likematthew/ExOrShock/3D Object/V2/Shaker.jpg

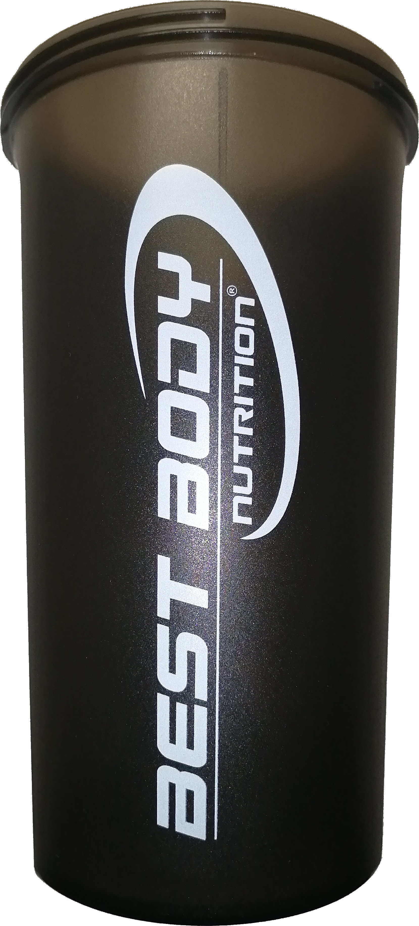
3D Object/V2/Shaker.jpg
