likematthew/ExOrShock/Project/Images/ex-or-shock-1-5-volt-battery-holder-2.jpg

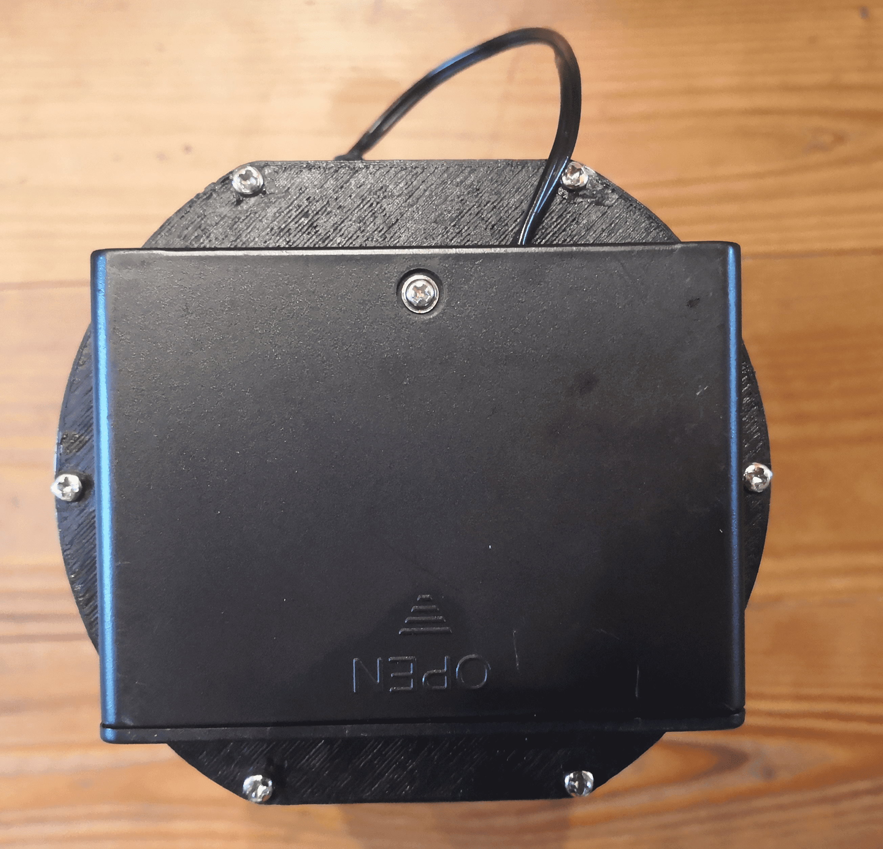
Project/Images/ex-or-shock-1-5-volt-battery-holder-2.jpg
