likematthew/ExOrShock/Project/Images/ex-or-shock-9-volt-battery-1.jpg

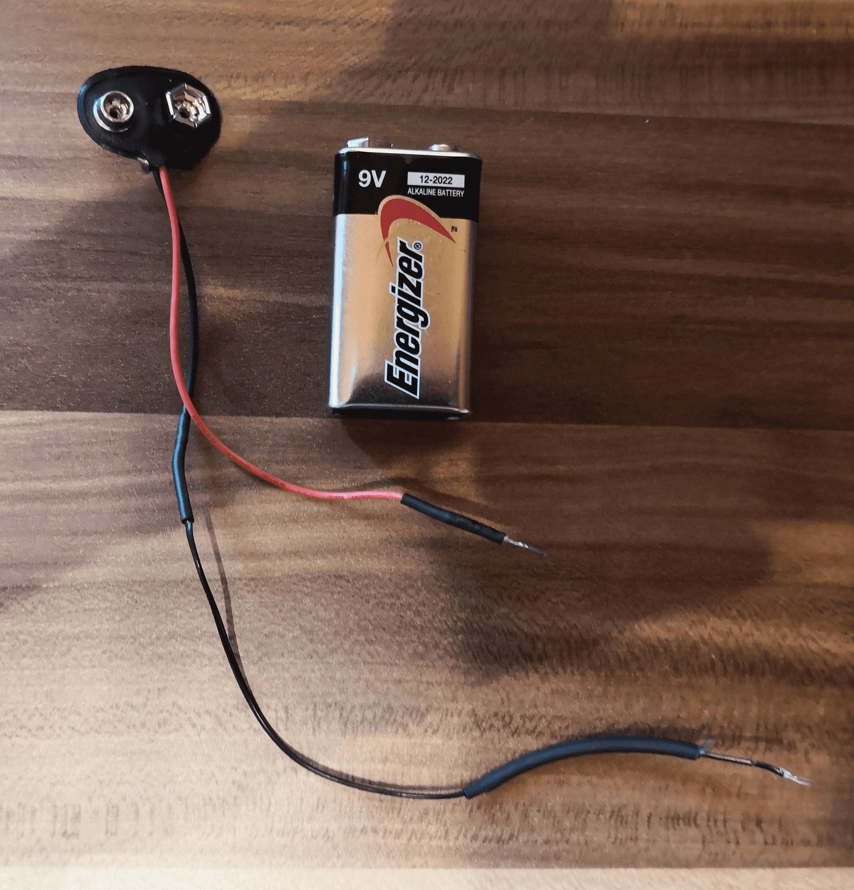
Project/Images/ex-or-shock-9-volt-battery-1.jpg
