likematthew/ExOrShock/Project/Images/ex-or-shock-cup-inside-1.jpg

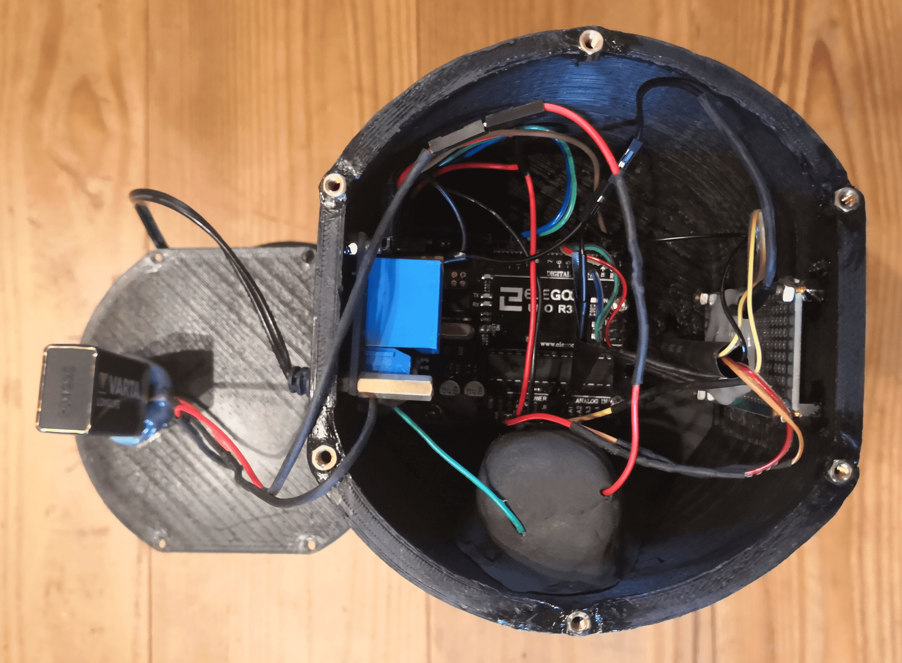
Project/Images/ex-or-shock-cup-inside-1.jpg
