likematthew/ExOrShock/Project/Images/ex-or-shock-cup-inside-2.jpg

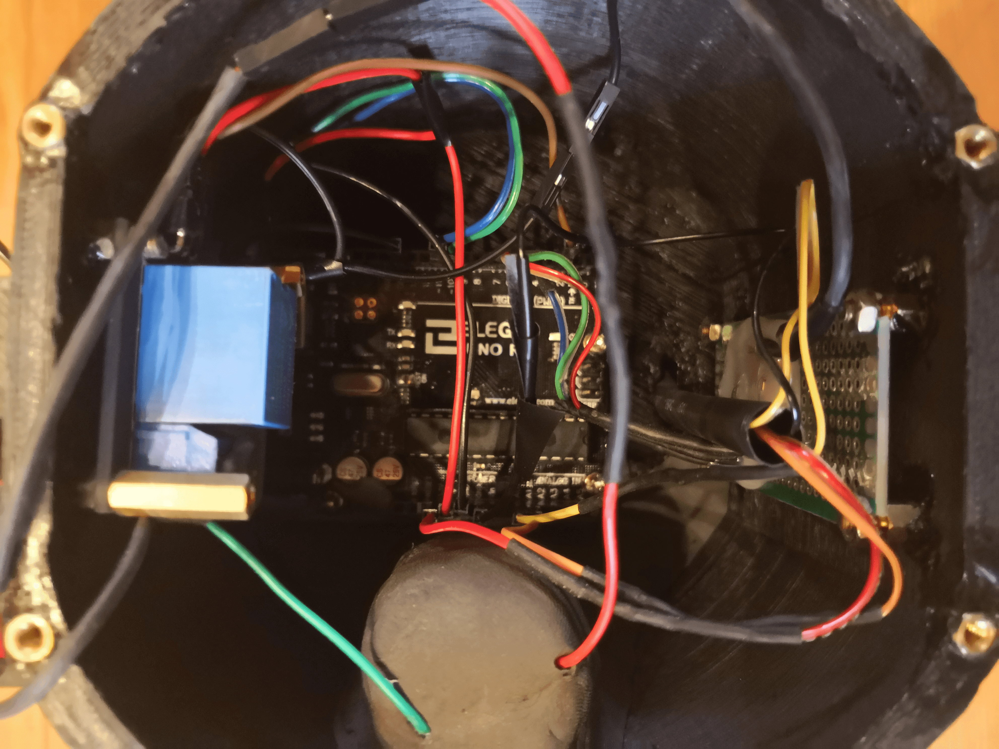
Project/Images/ex-or-shock-cup-inside-2.jpg
