likematthew/ExOrShock/Project/Images/ex-or-shock-cup-outside-1.jpg

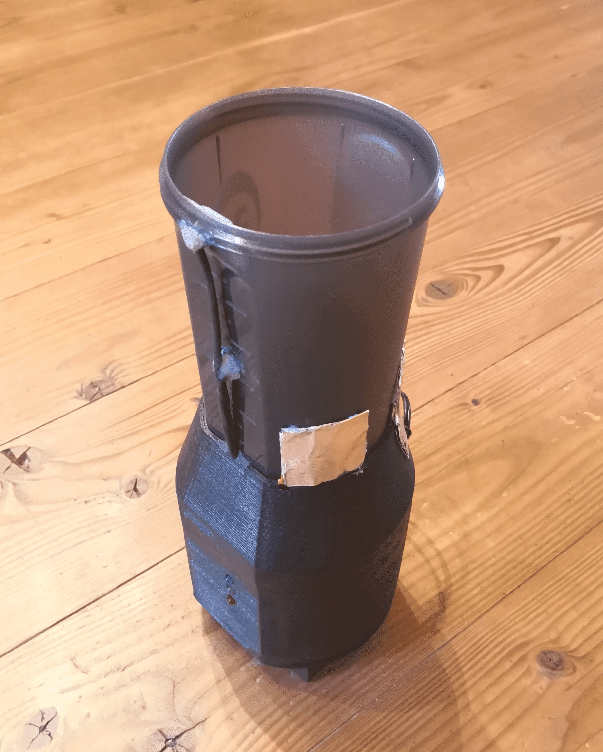
Project/Images/ex-or-shock-cup-outside-1.jpg
