likematthew/ExOrShock/Project/Images/ex-or-shock-fritzing-1.jpg

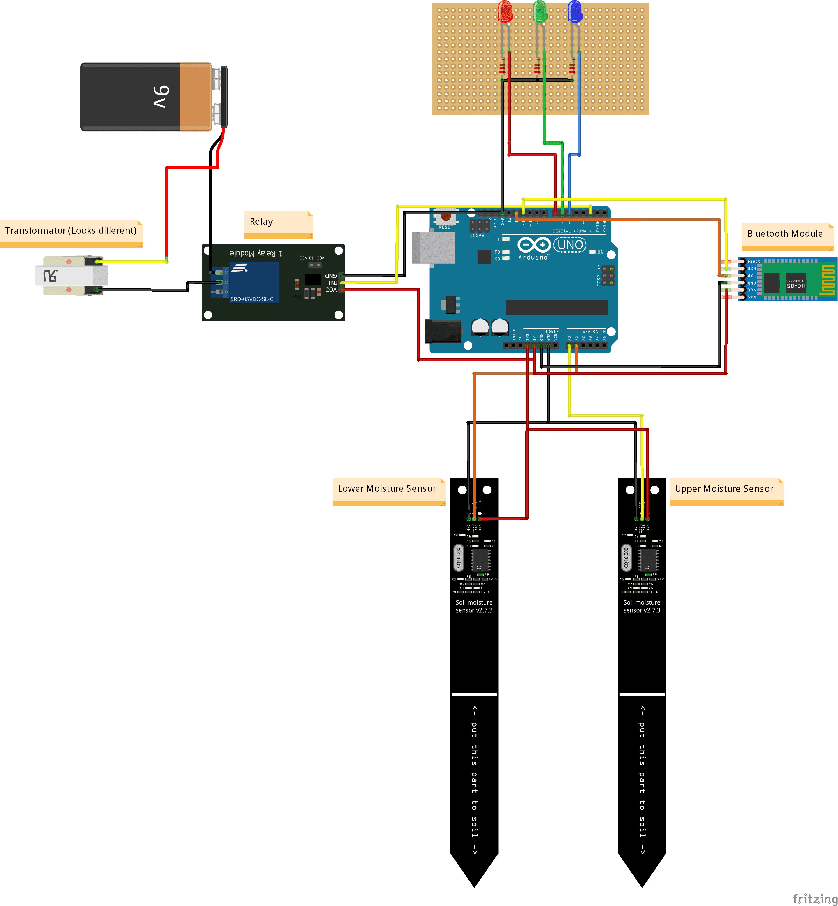
Project/Images/ex-or-shock-fritzing-1.jpg
