likematthew/ExOrShock/Project/Images/ex-or-shock-handle-1.jpg

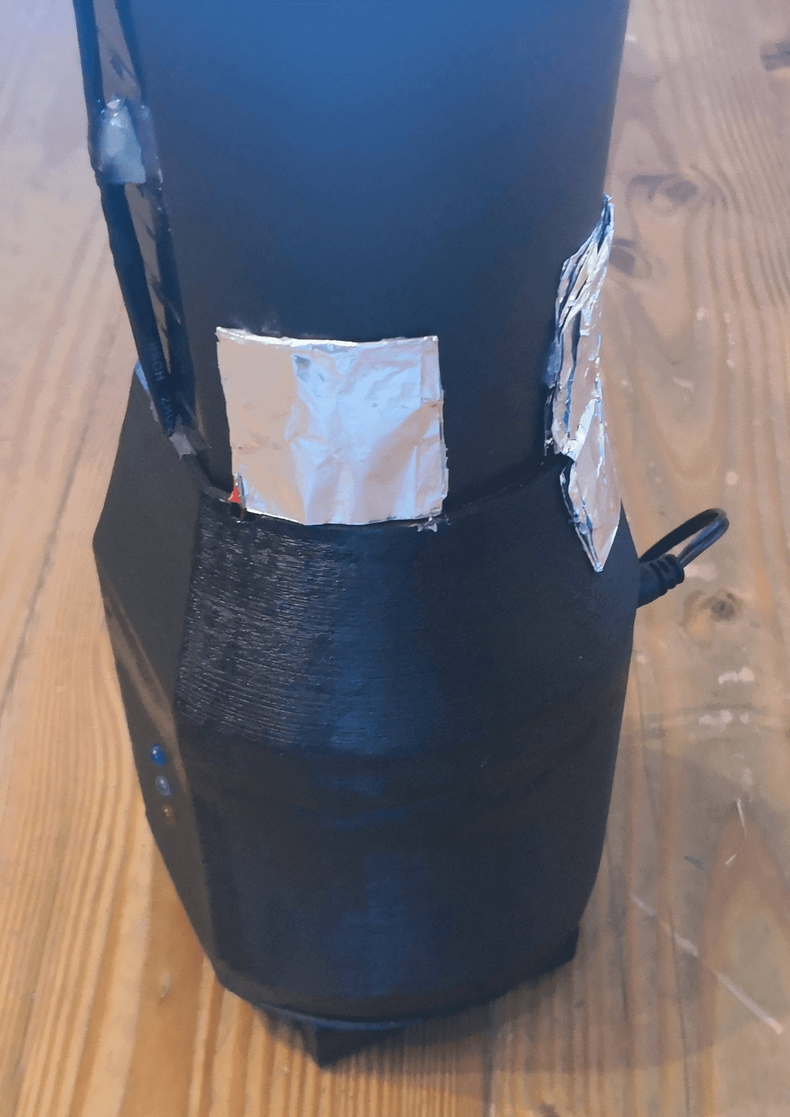
Project/Images/ex-or-shock-handle-1.jpg
