likematthew/ExOrShock/Project/Images/ex-or-shock-handle-2.jpg

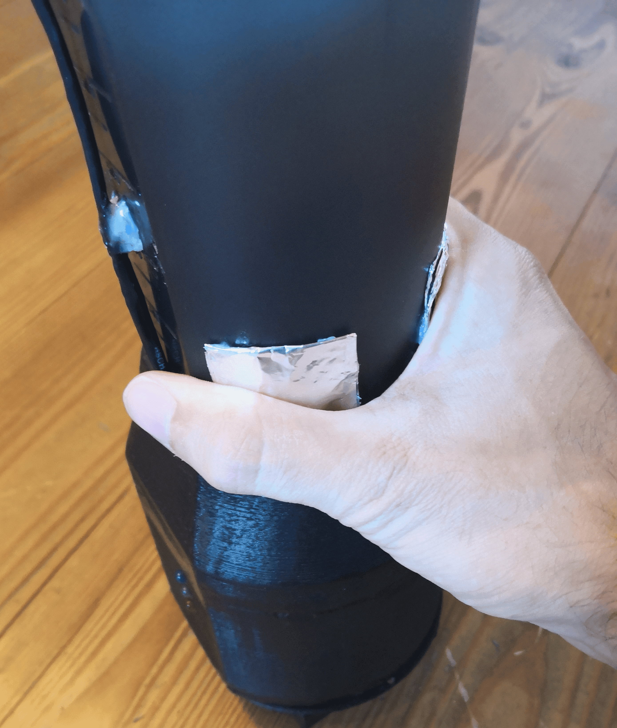
Project/Images/ex-or-shock-handle-2.jpg
