likematthew/ExOrShock/Project/Images/ex-or-shock-housing-1.jpg

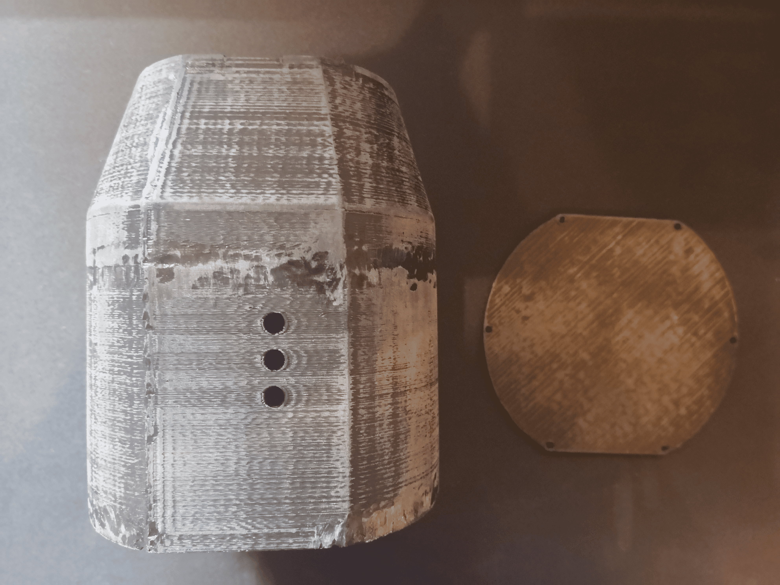
Project/Images/ex-or-shock-housing-1.jpg
