likematthew/ExOrShock/Project/Images/ex-or-shock-housing-2.jpg

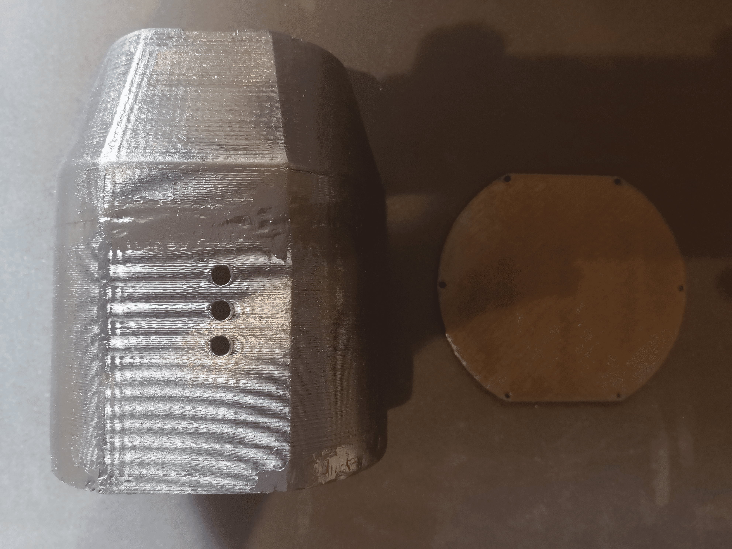
Project/Images/ex-or-shock-housing-2.jpg
