likematthew/ExOrShock/Project/Images/ex-or-shock-housing-moisture-level-sensor-2.jpg

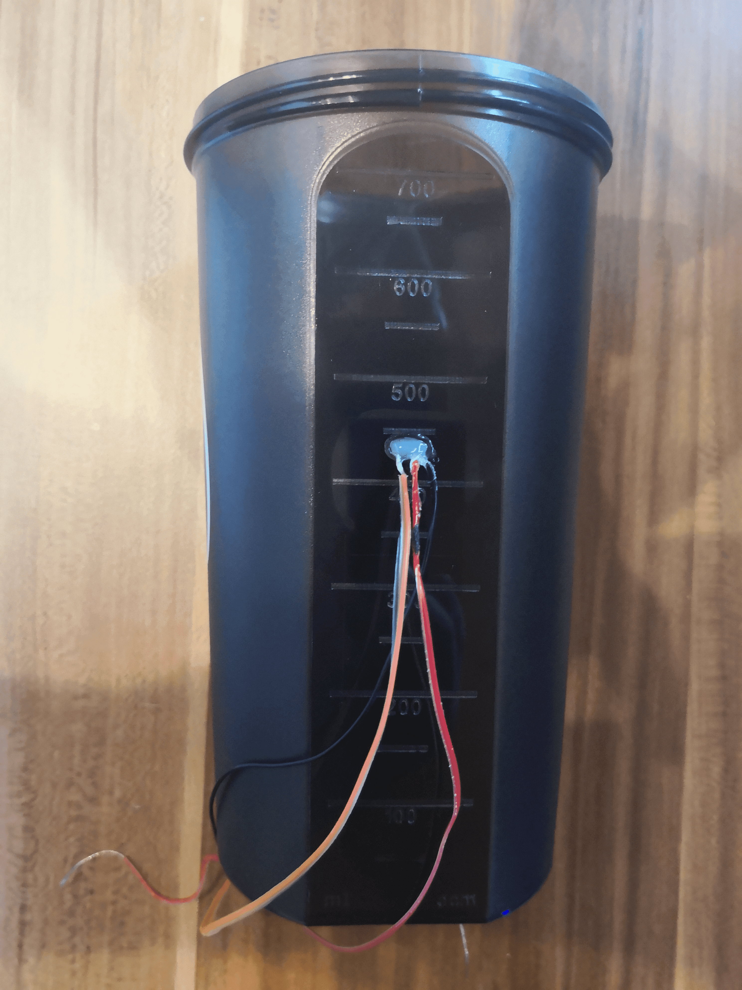
Project/Images/ex-or-shock-housing-moisture-level-sensor-2.jpg
