likematthew/ExOrShock/Project/Images/ex-or-shock-housing-threads-1.jpg

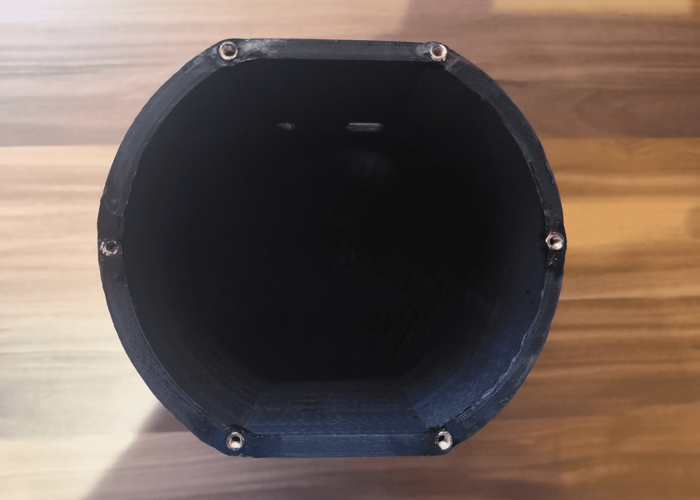
Project/Images/ex-or-shock-housing-threads-1.jpg
