likematthew/ExOrShock/Project/Images/ex-or-shock-housing-threads-3.jpg

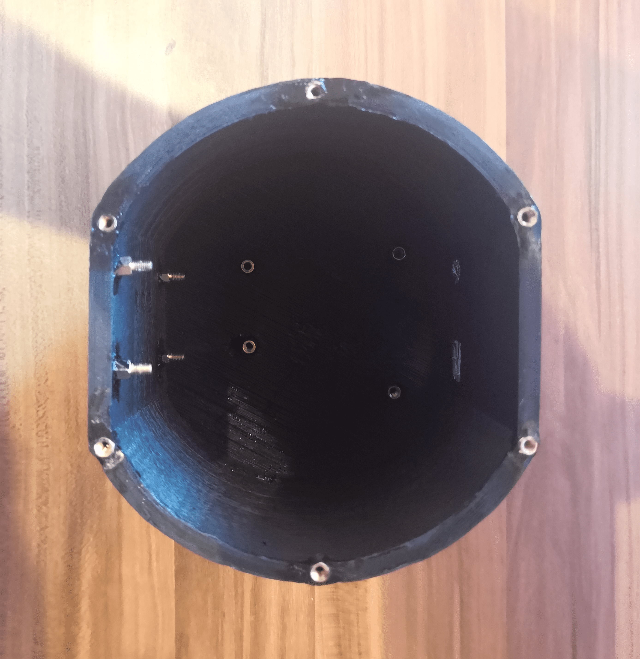
Project/Images/ex-or-shock-housing-threads-3.jpg
