likematthew/ExOrShock/Project/Images/ex-or-shock-housing-threads-4.jpg

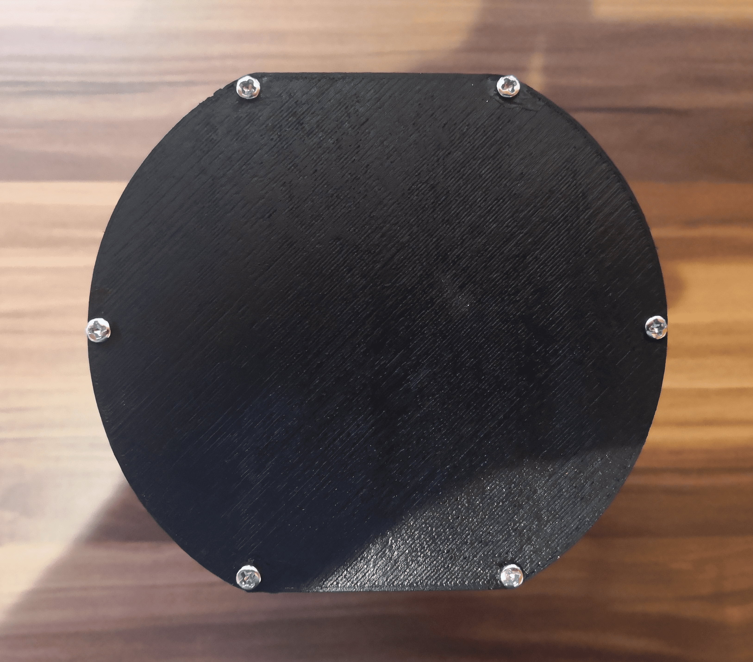
Project/Images/ex-or-shock-housing-threads-4.jpg
