likematthew/ExOrShock/Project/Images/ex-or-shock-jumper-cable-1.jpg

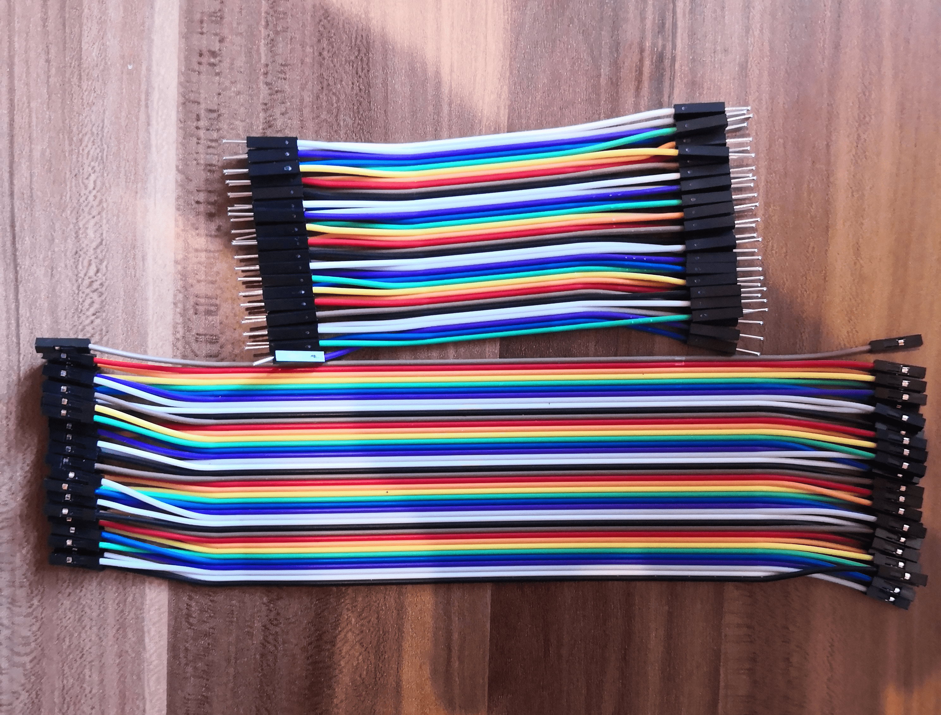
Project/Images/ex-or-shock-jumper-cable-1.jpg
