likematthew/ExOrShock/Project/Images/ex-or-shock-led-1.jpg

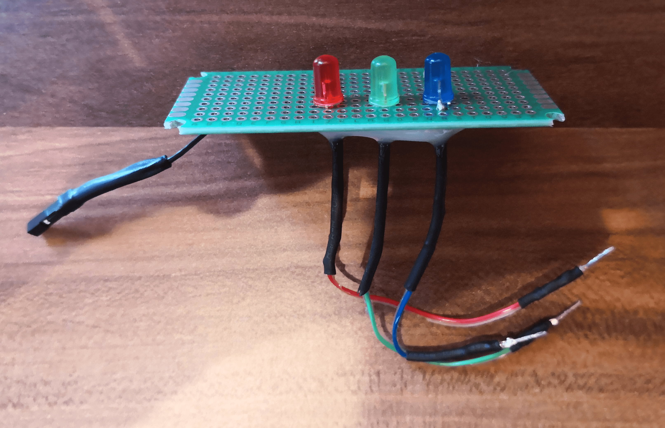
Project/Images/ex-or-shock-led-1.jpg
