likematthew/ExOrShock/Project/Images/ex-or-shock-led-2.jpg

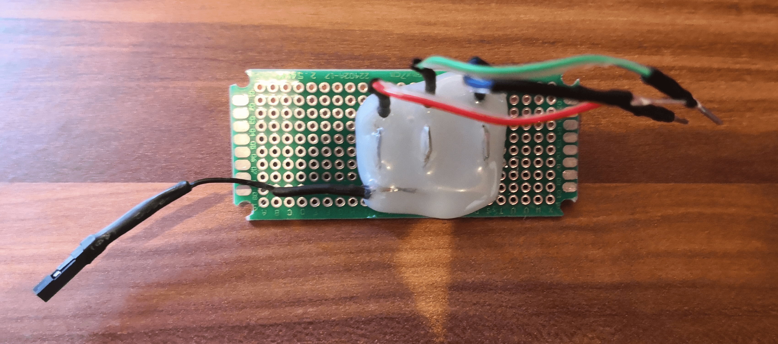
Project/Images/ex-or-shock-led-2.jpg
