likematthew/ExOrShock/Project/Images/ex-or-shock-moisture-level-sensor-1.jpg

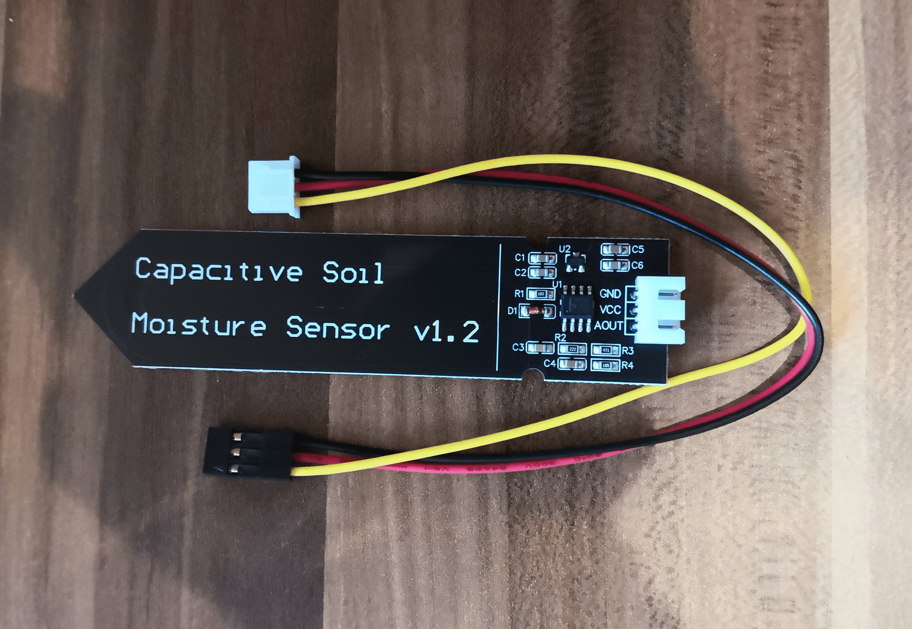
Project/Images/ex-or-shock-moisture-level-sensor-1.jpg
