likematthew/ExOrShock/Project/Images/ex-or-shock-moisture-level-sensor-3.jpg

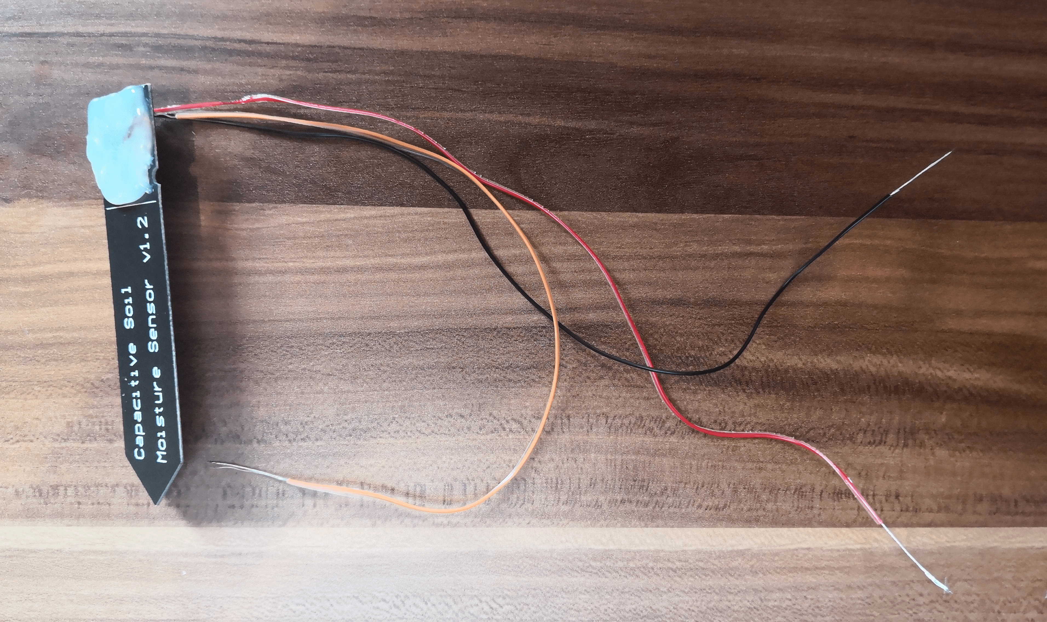
Project/Images/ex-or-shock-moisture-level-sensor-3.jpg
