likematthew/ExOrShock/Project/Images/ex-or-shock-moisture-level-sensor-4.jpg

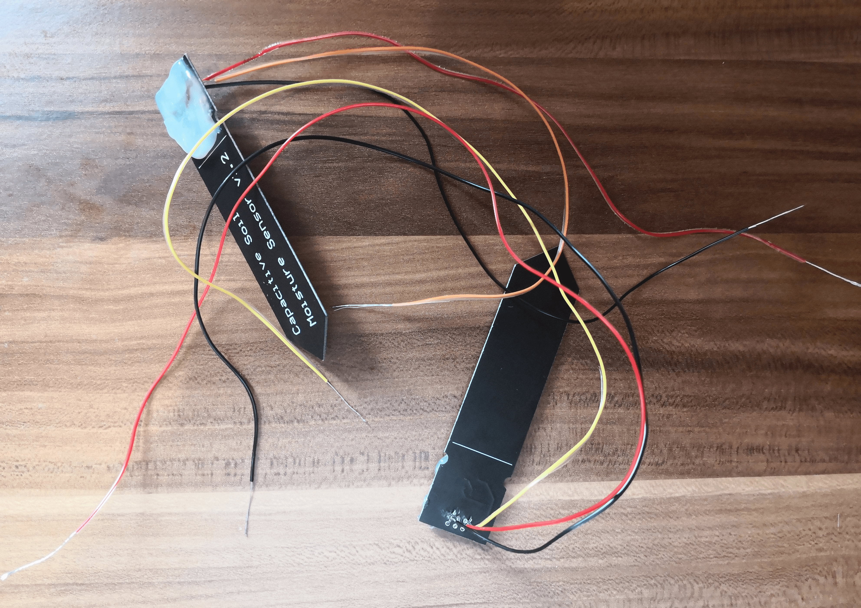
Project/Images/ex-or-shock-moisture-level-sensor-4.jpg
