likematthew/ExOrShock/Project/Images/ex-or-shock-program-1.jpg

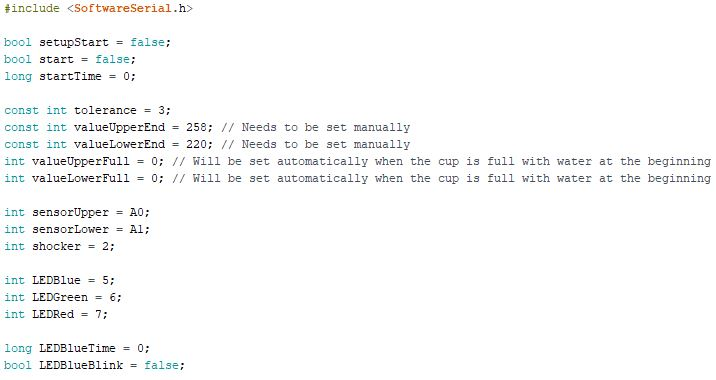
Project/Images/ex-or-shock-program-1.jpg
