likematthew/ExOrShock/Project/Images/ex-or-shock-relay-1.jpg

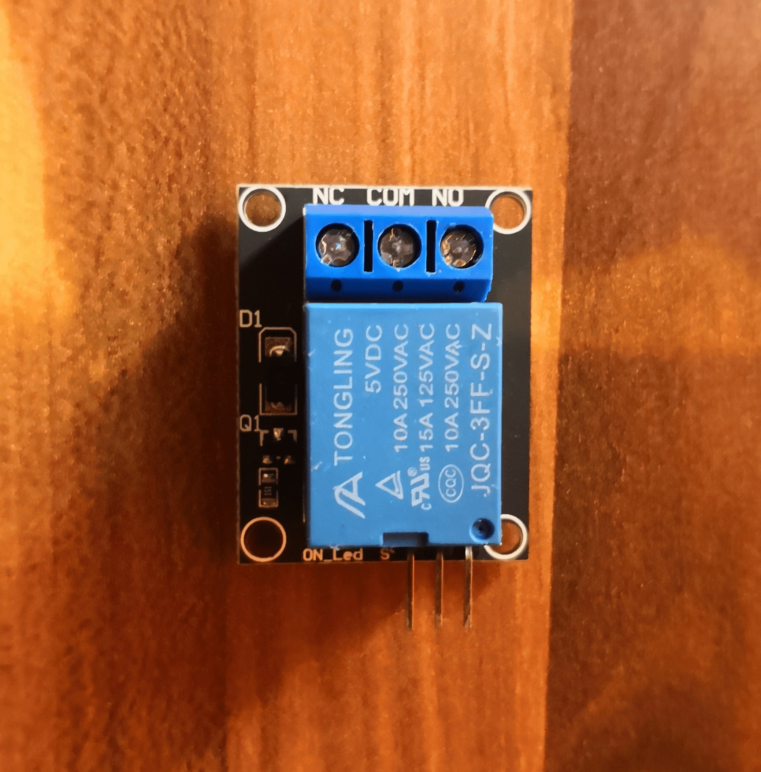
Project/Images/ex-or-shock-relay-1.jpg
