likematthew/ExOrShock/Project/Images/ex-or-shock-threads-1.jpg

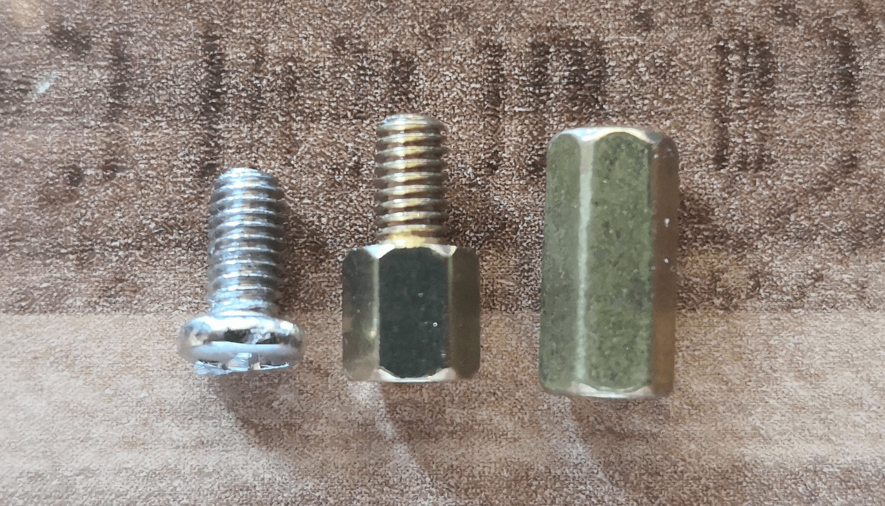
Project/Images/ex-or-shock-threads-1.jpg
